mohoyt/sthlmkb-storre/PCB/storre.kicad_sch

## KiCad design PCB/storre.kicad_sch (2023-10-12)

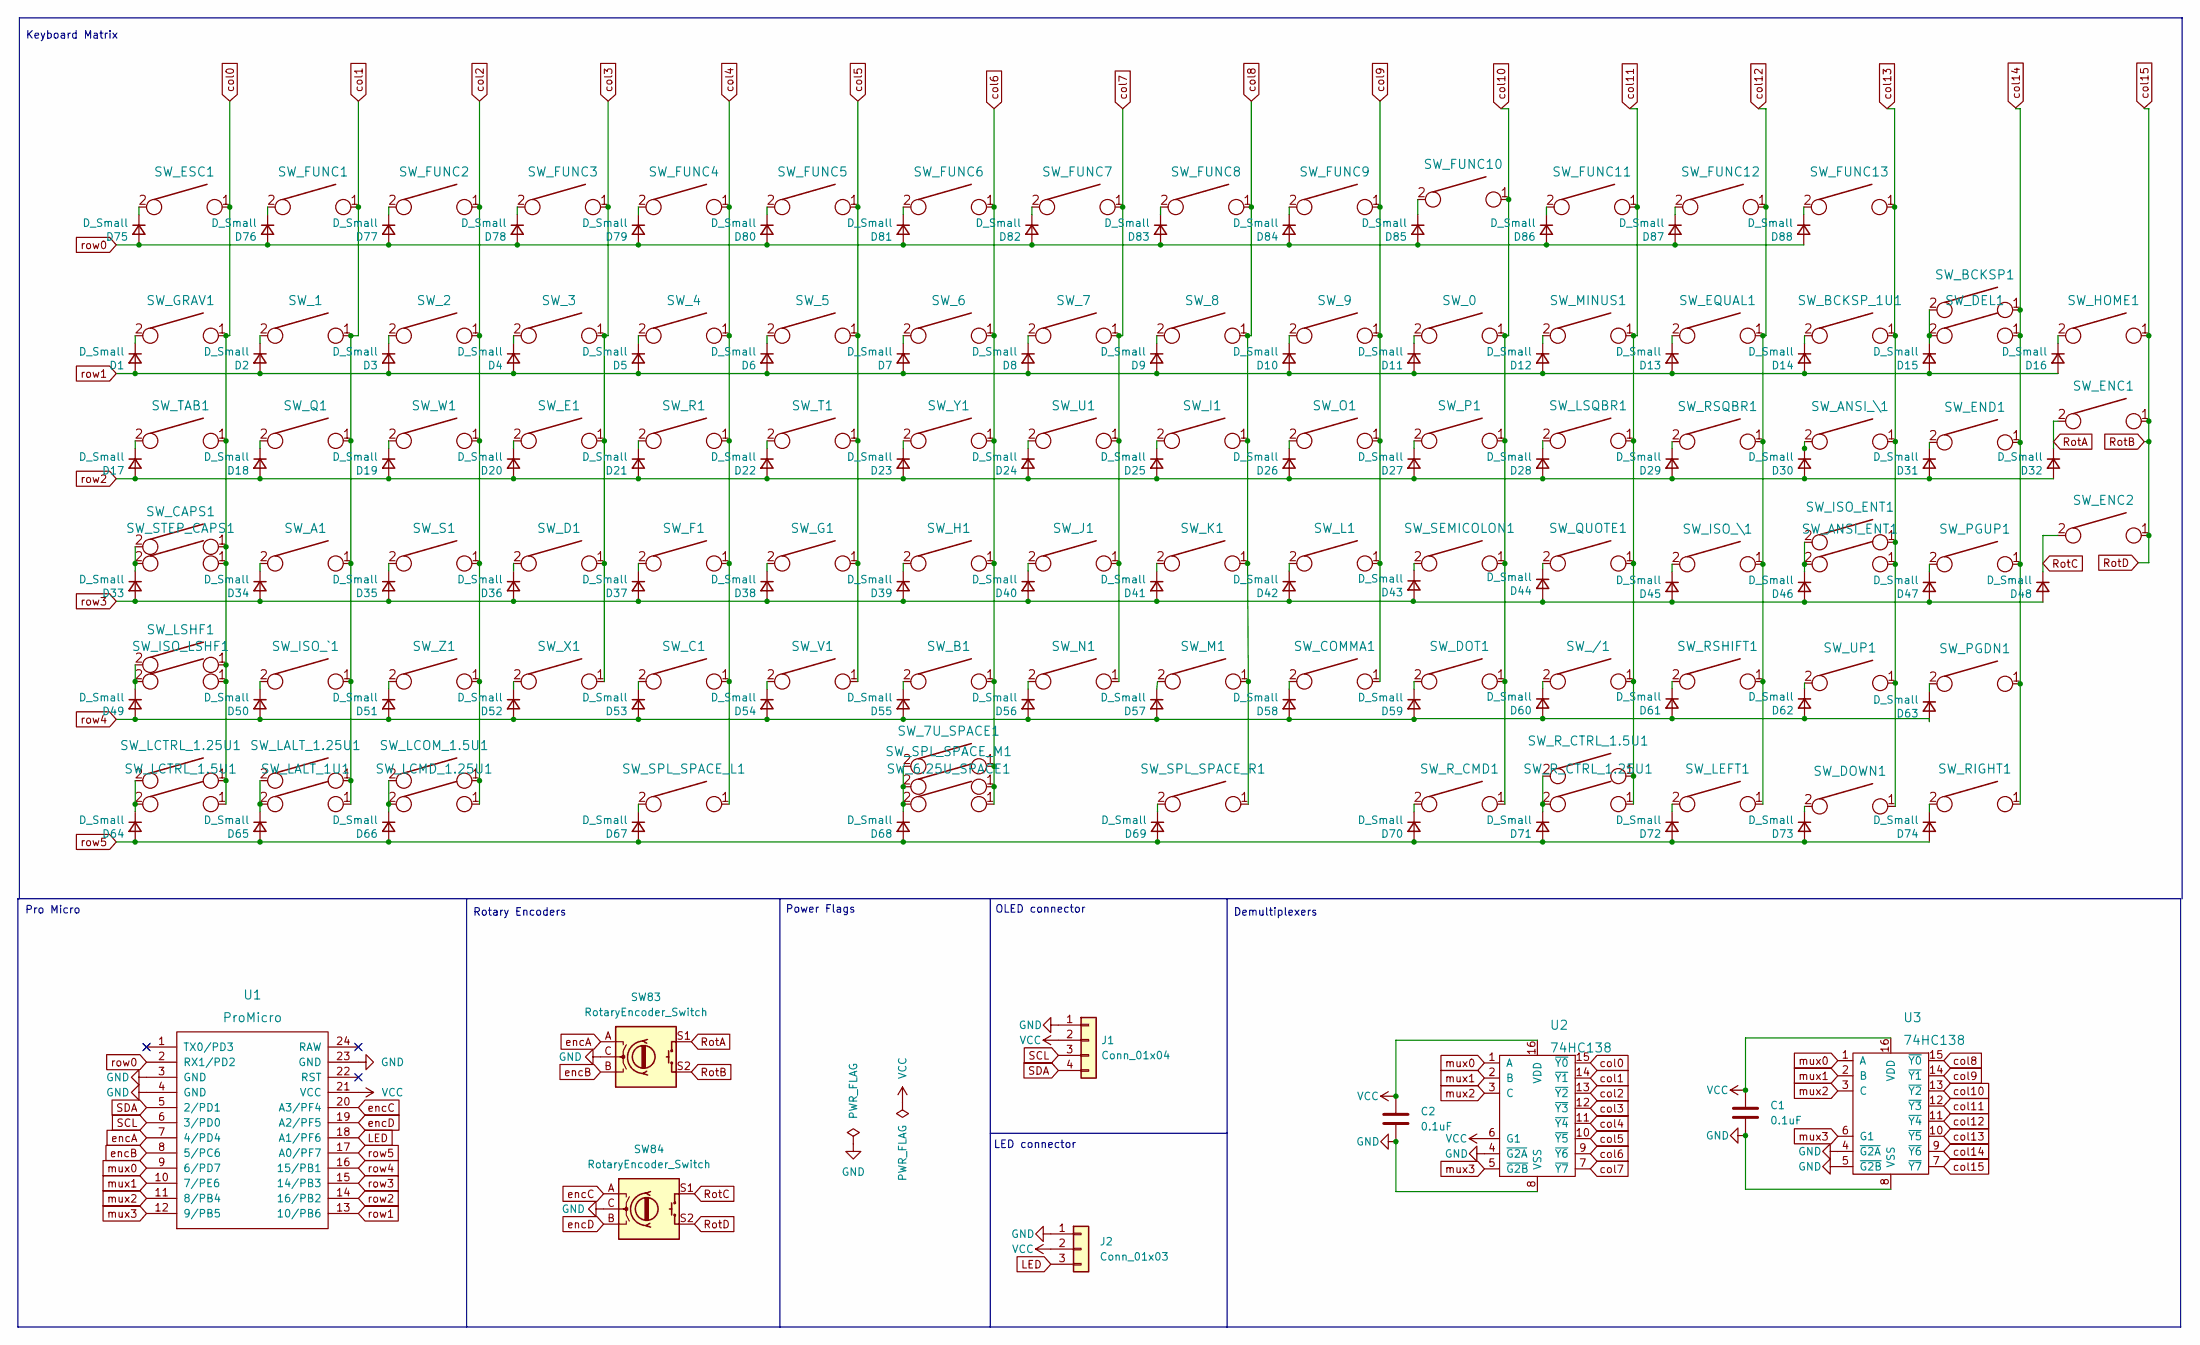
[picture p12: schematic storre.kicad_sch]

Parts:
C1, C2: 0.1uF; C_Disc_D4.7mm_W2.5mm_P5.00mm
D1, D2, D3, D4, D5, D6, D7, D8, D9, D10, D11, D12, D13, D14, D15, D16, D17, D18, D19, D20, D21, D22, D23, D24, D25, D26, D27, D28, D29, D30, D31, D32, D33, D34, D35, D36, D37, D38, D39, D40, D41, D42, D43, D44, D45, D46, D47, D48, D49, D50, D51, D52, D53, D54, D55, D56, D57, D58, D59, D60, D61, D62, D63, D64, D65, D66, D67, D68, D69, D70, D71, D72, D73, D74, D75, D76, D77, D78, D79, D80, D81, D82, D83, D84, D85, D86, D87, D88: D_Small; D_DO-34_SOD68_P7.62mm_Horizontal
J1: Conn_01x04; PinSocket_1x04_P2.54mm_Vertical
J2: Conn_01x03; PinSocket_1x03_P2.54mm_Vertical
SW83, SW84: RotaryEncoder_Switch; RotaryEncoder_EC11
SW_0, SW_1, SW_2, SW_3, SW_4, SW_5, SW_6, SW_7, SW_8, SW_9: KEYSW; SW_Cherry_MX_1.00u_PCB
SW_6.25U_SPACE1: KEYSW; SW_Cherry_MX_6.25u_PCB
SW_7U_SPACE1: KEYSW; SW_Cherry_MX_7u_PCB
SW_/1: KEYSW; SW_Cherry_MX_1.00u_PCB
SW_A1: KEYSW; SW_Cherry_MX_1.00u_PCB
SW_ANSI_ENT1: KEYSW; SW_Cherry_MX_2.25u_PCB
SW_ANSI_\1: KEYSW; SW_Cherry_MX_1.50u_PCB
SW_B1: KEYSW; SW_Cherry_MX_1.00u_PCB
SW_BCKSP1: KEYSW; SW_Cherry_MX_2.00u_PCB
SW_BCKSP_1U1: KEYSW; SW_Cherry_MX_1.00u_PCB
SW_C1: KEYSW; SW_Cherry_MX_1.00u_PCB
SW_CAPS1: KEYSW; SW_Cherry_MX_1.75u_PCB
SW_COMMA1: KEYSW; SW_Cherry_MX_1.00u_PCB
SW_D1: KEYSW; SW_Cherry_MX_1.00u_PCB
SW_DEL1: KEYSW; SW_Cherry_MX_1.00u_PCB
SW_DOT1: KEYSW; SW_Cherry_MX_1.00u_PCB
SW_DOWN1: KEYSW; SW_Cherry_MX_1.00u_PCB
SW_E1: KEYSW; SW_Cherry_MX_1.00u_PCB
SW_ENC1, SW_ENC2: KEYSW; SW_Cherry_MX_1.00u_PCB
SW_END1: KEYSW; SW_Cherry_MX_1.00u_PCB
SW_EQUAL1: KEYSW; SW_Cherry_MX_1.00u_PCB
SW_ESC1: KEYSW; SW_Cherry_MX_1.00u_PCB
SW_F1: KEYSW; SW_Cherry_MX_1.00u_PCB
SW_FUNC1, SW_FUNC2, SW_FUNC3, SW_FUNC4, SW_FUNC5, SW_FUNC6, SW_FUNC7, SW_FUNC8, SW_FUNC9, SW_FUNC10, SW_FUNC11, SW_FUNC12, SW_FUNC13: KEYSW; SW_Cherry_MX_1.00u_PCB
SW_G1: KEYSW; SW_Cherry_MX_1.00u_PCB
SW_GRAV1: KEYSW; SW_Cherry_MX_1.00u_PCB
SW_H1: KEYSW; SW_Cherry_MX_1.00u_PCB
SW_HOME1: KEYSW; SW_Cherry_MX_1.00u_PCB
SW_I1: KEYSW; SW_Cherry_MX_1.00u_PCB
SW_ISO_ENT1: KEYSW; SW_Cherry_MX_ISOEnter_PCB_Flipped_Rotated
SW_ISO_LSHF1: KEYSW; SW_Cherry_MX_1.25u_PCB
SW_ISO_\1: KEYSW; SW_Cherry_MX_1.00u_PCB
SW_ISO_`1: KEYSW; SW_Cherry_MX_1.00u_PCB
SW_J1: KEYSW; SW_Cherry_MX_1.00u_PCB
SW_K1: KEYSW; SW_Cherry_MX_1.00u_PCB
SW_L1: KEYSW; SW_Cherry_MX_1.00u_PCB
SW_LALT_1.25U1: KEYSW; SW_Cherry_MX_1.25u_PCB
SW_LALT_1U1: KEYSW; SW_Cherry_MX_1.00u_PCB
SW_LCMD_1.25U1: KEYSW; SW_Cherry_MX_1.25u_PCB
SW_LCOM_1.5U1: KEYSW; SW_Cherry_MX_1.50u_PCB
SW_LCTRL_1.5U1: KEYSW; SW_Cherry_MX_1.50u_PCB
SW_LCTRL_1.25U1: KEYSW; SW_Cherry_MX_1.25u_PCB
SW_LEFT1: KEYSW; SW_Cherry_MX_1.00u_PCB
SW_LSHF1: KEYSW; SW_Cherry_MX_2.25u_PCB
SW_LSQBR1: KEYSW; SW_Cherry_MX_1.00u_PCB
SW_M1: KEYSW; SW_Cherry_MX_1.00u_PCB
SW_MINUS1: KEYSW; SW_Cherry_MX_1.00u_PCB
SW_N1: KEYSW; SW_Cherry_MX_1.00u_PCB
SW_O1: KEYSW; SW_Cherry_MX_1.00u_PCB
SW_P1: KEYSW; SW_Cherry_MX_1.00u_PCB
SW_PGDN1: KEYSW; SW_Cherry_MX_1.00u_PCB
SW_PGUP1: KEYSW; SW_Cherry_MX_1.00u_PCB
SW_Q1: KEYSW; SW_Cherry_MX_1.00u_PCB
SW_QUOTE1: KEYSW; SW_Cherry_MX_1.00u_PCB
SW_R1: KEYSW; SW_Cherry_MX_1.00u_PCB
SW_RIGHT1: KEYSW; SW_Cherry_MX_1.00u_PCB
SW_RSHIFT1: KEYSW; SW_Cherry_MX_1.75u_PCB
SW_RSQBR1: KEYSW; SW_Cherry_MX_1.00u_PCB
SW_R_CMD1: KEYSW; SW_Cherry_MX_1.25u_PCB
SW_R_CTRL_1.5U1: KEYSW; SW_Cherry_MX_1.50u_PCB
SW_R_CTRL_1.25U1: KEYSW; SW_Cherry_MX_1.25u_PCB
SW_S1: KEYSW; SW_Cherry_MX_1.00u_PCB
SW_SEMICOLON1: KEYSW; SW_Cherry_MX_1.00u_PCB
SW_SPL_SPACE_L1: KEYSW; SW_Cherry_MX_2.25u_PCB
SW_SPL_SPACE_M1: KEYSW; SW_Cherry_MX_1.25u_PCB
SW_SPL_SPACE_R1: KEYSW; SW_Cherry_MX_2.75u_PCB
SW_STEP_CAPS1: KEYSW; SW_Cherry_MX_1.25u_PCB
SW_T1: KEYSW; SW_Cherry_MX_1.00u_PCB
SW_TAB1: KEYSW; SW_Cherry_MX_1.50u_PCB
SW_U1: KEYSW; SW_Cherry_MX_1.00u_PCB
SW_UP1: KEYSW; SW_Cherry_MX_1.00u_PCB
SW_V1: KEYSW; SW_Cherry_MX_1.00u_PCB
SW_W1: KEYSW; SW_Cherry_MX_1.00u_PCB
SW_X1: KEYSW; SW_Cherry_MX_1.00u_PCB
SW_Y1: KEYSW; SW_Cherry_MX_1.00u_PCB
SW_Z1: KEYSW; SW_Cherry_MX_1.00u_PCB
U1: ProMicro; ArduinoProMicro-ZigZag
U2, U3: 74HC138; DIP-16_W7.62mm_Socket

Connections:
GND: C1.2, C2.2, J1.1, J2.1, SW83.C, SW84.C, U1.3 (GND), U1.4 (GND), U1.23 (GND), U2.4 (~G2A), U2.8 (VSS), U3.4 (~G2A), U3.5 (~G2B), U3.8 (VSS)
LED: J2.3, U1.18 (A1/PF6)
unnamed: D1.1 (K), SW_GRAV1.2
unnamed: D2.1 (K), SW_1.2
unnamed: D3.1 (K), SW_2.2
unnamed: D4.1 (K), SW_3.2
unnamed: D5.1 (K), SW_4.2
unnamed: D6.1 (K), SW_5.2
unnamed: D7.1 (K), SW_6.2
unnamed: D8.1 (K), SW_7.2
unnamed: D9.1 (K), SW_8.2
unnamed: D10.1 (K), SW_9.2
unnamed: D11.1 (K), SW_0.2
unnamed: D12.1 (K), SW_MINUS1.2
unnamed: D13.1 (K), SW_EQUAL1.2
unnamed: D14.1 (K), SW_BCKSP_1U1.2
unnamed: D15.1 (K), SW_BCKSP1.2, SW_DEL1.2
unnamed: D16.1 (K), SW_HOME1.2
unnamed: D17.1 (K), SW_TAB1.2
unnamed: D18.1 (K), SW_Q1.2
unnamed: D19.1 (K), SW_W1.2
unnamed: D20.1 (K), SW_E1.2
unnamed: D21.1 (K), SW_R1.2
unnamed: D22.1 (K), SW_T1.2
unnamed: D23.1 (K), SW_Y1.2
unnamed: D24.1 (K), SW_U1.2
unnamed: D25.1 (K), SW_I1.2
unnamed: D26.1 (K), SW_O1.2
unnamed: D27.1 (K), SW_P1.2
unnamed: D28.1 (K), SW_LSQBR1.2
unnamed: D29.1 (K), SW_RSQBR1.2
unnamed: D30.1 (K), SW_ANSI_\1.2
unnamed: D31.1 (K), SW_END1.2
unnamed: D33.1 (K), SW_CAPS1.2, SW_STEP_CAPS1.2
unnamed: D34.1 (K), SW_A1.2
unnamed: D35.1 (K), SW_S1.2
unnamed: D36.1 (K), SW_D1.2
unnamed: D37.1 (K), SW_F1.2
unnamed: D38.1 (K), SW_G1.2
unnamed: D39.1 (K), SW_H1.2
unnamed: D40.1 (K), SW_J1.2
unnamed: D41.1 (K), SW_K1.2
unnamed: D42.1 (K), SW_L1.2
unnamed: D43.1 (K), SW_SEMICOLON1.2
unnamed: D44.1 (K), SW_QUOTE1.2
unnamed: D45.1 (K), SW_ISO_\1.2
unnamed: D46.1 (K), SW_ANSI_ENT1.2, SW_ISO_ENT1.2
unnamed: D47.1 (K), SW_PGUP1.2
unnamed: D49.1 (K), SW_ISO_LSHF1.2, SW_LSHF1.2
unnamed: D50.1 (K), SW_ISO_`1.2
unnamed: D51.1 (K), SW_Z1.2
unnamed: D52.1 (K), SW_X1.2
unnamed: D53.1 (K), SW_C1.2
unnamed: D54.1 (K), SW_V1.2
unnamed: D55.1 (K), SW_B1.2
unnamed: D56.1 (K), SW_N1.2
unnamed: D57.1 (K), SW_M1.2
unnamed: D58.1 (K), SW_COMMA1.2
unnamed: D59.1 (K), SW_DOT1.2
unnamed: D60.1 (K), SW_/1.2
unnamed: D61.1 (K), SW_RSHIFT1.2
unnamed: D62.1 (K), SW_UP1.2
unnamed: D63.1 (K), SW_PGDN1.2
unnamed: D64.1 (K), SW_LCTRL_1.5U1.2, SW_LCTRL_1.25U1.2
unnamed: D65.1 (K), SW_LALT_1.25U1.2, SW_LALT_1U1.2
unnamed: D66.1 (K), SW_LCMD_1.25U1.2, SW_LCOM_1.5U1.2
unnamed: D67.1 (K), SW_SPL_SPACE_L1.2
unnamed: D68.1 (K), SW_6.25U_SPACE1.2, SW_7U_SPACE1.2, SW_SPL_SPACE_M1.2
unnamed: D69.1 (K), SW_SPL_SPACE_R1.2
unnamed: D70.1 (K), SW_R_CMD1.2
unnamed: D71.1 (K), SW_R_CTRL_1.5U1.2, SW_R_CTRL_1.25U1.2
unnamed: D72.1 (K), SW_LEFT1.2
unnamed: D73.1 (K), SW_DOWN1.2
unnamed: D74.1 (K), SW_RIGHT1.2
unnamed: D75.1 (K), SW_ESC1.2
unnamed: D76.1 (K), SW_FUNC1.2
unnamed: D77.1 (K), SW_FUNC2.2
unnamed: D78.1 (K), SW_FUNC3.2
unnamed: D79.1 (K), SW_FUNC4.2
unnamed: D80.1 (K), SW_FUNC5.2
unnamed: D81.1 (K), SW_FUNC6.2
unnamed: D82.1 (K), SW_FUNC7.2
unnamed: D83.1 (K), SW_FUNC8.2
unnamed: D84.1 (K), SW_FUNC9.2
unnamed: D85.1 (K), SW_FUNC10.2
unnamed: D86.1 (K), SW_FUNC11.2
unnamed: D87.1 (K), SW_FUNC12.2
unnamed: D88.1 (K), SW_FUNC13.2
RotA: D32.1 (K), SW83.S1, SW_ENC1.2
RotC: D48.1 (K), SW84.S1, SW_ENC2.2
SCL: J1.3, U1.6 (3/PD0)
SDA: J1.4, U1.5 (2/PD1)
VCC: C1.1, C2.1, J1.2, J2.2, U1.21 (VCC), U2.6 (G1), U2.16 (VDD), U3.16 (VDD)
col0: SW_CAPS1.1, SW_ESC1.1, SW_GRAV1.1, SW_ISO_LSHF1.1, SW_LCTRL_1.5U1.1, SW_LCTRL_1.25U1.1, SW_LSHF1.1, SW_STEP_CAPS1.1, SW_TAB1.1, U2.15 (~Y0)
col1: SW_1.1, SW_A1.1, SW_FUNC1.1, SW_ISO_`1.1, SW_LALT_1.25U1.1, SW_LALT_1U1.1, SW_Q1.1, U2.14 (~Y1)
col2: SW_2.1, SW_FUNC2.1, SW_LCMD_1.25U1.1, SW_LCOM_1.5U1.1, SW_S1.1, SW_W1.1, SW_Z1.1, U2.13 (~Y2)
col3: SW_3.1, SW_D1.1, SW_E1.1, SW_FUNC3.1, SW_X1.1, U2.12 (~Y3)
col4: SW_4.1, SW_C1.1, SW_F1.1, SW_FUNC4.1, SW_R1.1, SW_SPL_SPACE_L1.1, U2.11 (~Y4)
col5: SW_5.1, SW_FUNC5.1, SW_G1.1, SW_T1.1, SW_V1.1, U2.10 (~Y5)
col6: SW_6.1, SW_6.25U_SPACE1.1, SW_7U_SPACE1.1, SW_B1.1, SW_FUNC6.1, SW_H1.1, SW_SPL_SPACE_M1.1, SW_Y1.1, U2.9 (~Y6)
col7: SW_7.1, SW_FUNC7.1, SW_J1.1, SW_N1.1, SW_U1.1, U2.7 (~Y7)
col8: SW_8.1, SW_FUNC8.1, SW_I1.1, SW_K1.1, SW_M1.1, SW_SPL_SPACE_R1.1, U3.15 (~Y0)
col9: SW_9.1, SW_COMMA1.1, SW_FUNC9.1, SW_L1.1, SW_O1.1, U3.14 (~Y1)
col10: SW_0.1, SW_DOT1.1, SW_FUNC10.1, SW_P1.1, SW_R_CMD1.1, SW_SEMICOLON1.1, U3.13 (~Y2)
col11: SW_/1.1, SW_FUNC11.1, SW_LSQBR1.1, SW_MINUS1.1, SW_QUOTE1.1, SW_R_CTRL_1.5U1.1, SW_R_CTRL_1.25U1.1, U3.12 (~Y3)
col12: SW_EQUAL1.1, SW_FUNC12.1, SW_ISO_\1.1, SW_LEFT1.1, SW_RSHIFT1.1, SW_RSQBR1.1, U3.11 (~Y4)
col13: SW_ANSI_ENT1.1, SW_ANSI_\1.1, SW_BCKSP_1U1.1, SW_DOWN1.1, SW_FUNC13.1, SW_ISO_ENT1.1, SW_UP1.1, U3.10 (~Y5)
col14: SW_BCKSP1.1, SW_DEL1.1, SW_END1.1, SW_PGDN1.1, SW_PGUP1.1, SW_RIGHT1.1, U3.9 (~Y6)
col15: SW83.S2, SW84.S2, SW_ENC1.1, SW_ENC2.1, SW_HOME1.1, U3.7 (~Y7)
encA: SW83.A, U1.7 (4/PD4)
encB: SW83.B, U1.8 (5/PC6)
encC: SW84.A, U1.20 (A3/PF4)
encD: SW84.B, U1.19 (A2/PF5)
mux0: U1.9 (6/PD7), U2.1 (A), U3.1 (A)
mux1: U1.10 (7/PE6), U2.2 (B), U3.2 (B)
mux2: U1.11 (8/PB4), U2.3 (C), U3.3 (C)
mux3: U1.12 (9/PB5), U2.5 (~G2B), U3.6 (G1)
row0: D75.2 (A), D76.2 (A), D77.2 (A), D78.2 (A), D79.2 (A), D80.2 (A), D81.2 (A), D82.2 (A), D83.2 (A), D84.2 (A), D85.2 (A), D86.2 (A), D87.2 (A), D88.2 (A), U1.2 (RX1/PD2)
row1: D1.2 (A), D2.2 (A), D3.2 (A), D4.2 (A), D5.2 (A), D6.2 (A), D7.2 (A), D8.2 (A), D9.2 (A), D10.2 (A), D11.2 (A), D12.2 (A), D13.2 (A), D14.2 (A), D15.2 (A), D16.2 (A), U1.13 (10/PB6)
row2: D17.2 (A), D18.2 (A), D19.2 (A), D20.2 (A), D21.2 (A), D22.2 (A), D23.2 (A), D24.2 (A), D25.2 (A), D26.2 (A), D27.2 (A), D28.2 (A), D29.2 (A), D30.2 (A), D31.2 (A), D32.2 (A), U1.14 (16/PB2)
row3: D33.2 (A), D34.2 (A), D35.2 (A), D36.2 (A), D37.2 (A), D38.2 (A), D39.2 (A), D40.2 (A), D41.2 (A), D42.2 (A), D43.2 (A), D44.2 (A), D45.2 (A), D46.2 (A), D47.2 (A), D48.2 (A), U1.15 (14/PB3)
row4: D49.2 (A), D50.2 (A), D51.2 (A), D52.2 (A), D53.2 (A), D54.2 (A), D55.2 (A), D56.2 (A), D57.2 (A), D58.2 (A), D59.2 (A), D60.2 (A), D61.2 (A), D62.2 (A), D63.2 (A), U1.16 (15/PB1)
row5: D64.2 (A), D65.2 (A), D66.2 (A), D67.2 (A), D68.2 (A), D69.2 (A), D70.2 (A), D71.2 (A), D72.2 (A), D73.2 (A), D74.2 (A), U1.17 (A0/PF7)

Notes on the sheet:
OLED connector
Rotary Encoders
Keyboard Matrix
Power Flags
LED connector
Pro Micro
Demultiplexers
